sboysel/clyde/img/PXL_20231121_120252323.jpg

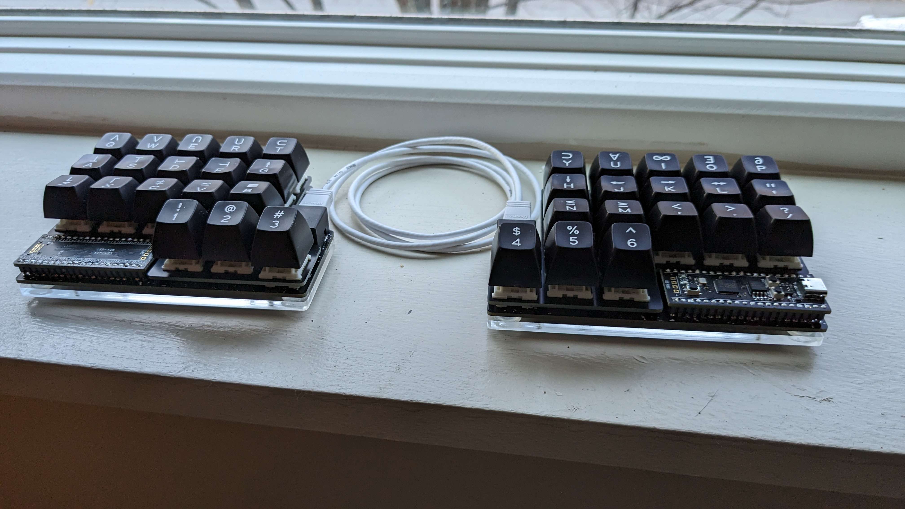
img/PXL_20231121_120252323.jpg
