sboysel/clyde/img/PXL_20231121_120302832.jpg

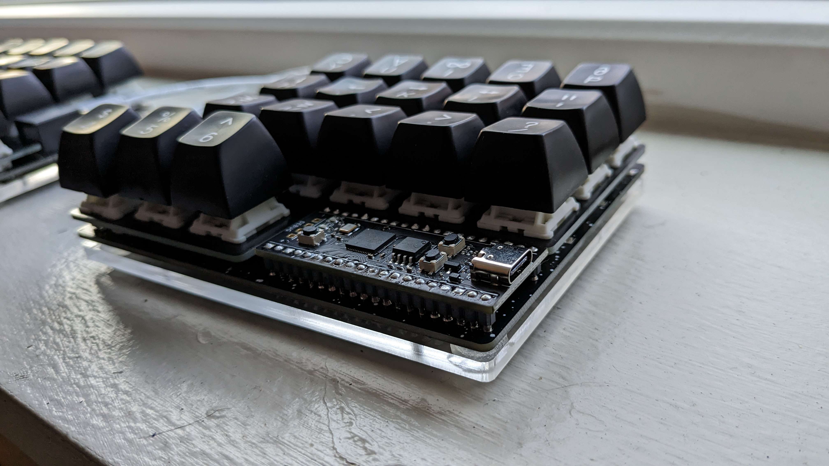
img/PXL_20231121_120302832.jpg
