sboysel/clyde/img/PXL_20231121_120807884.jpg

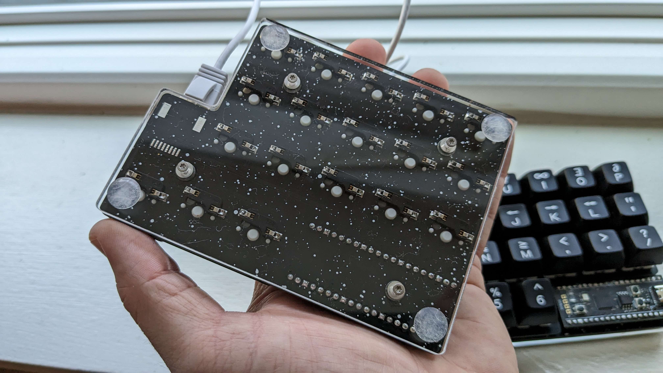
img/PXL_20231121_120807884.jpg
